thomasdevine01/cmkc-keyboard/Pages/Docs/Images/IMG-2283.jpg

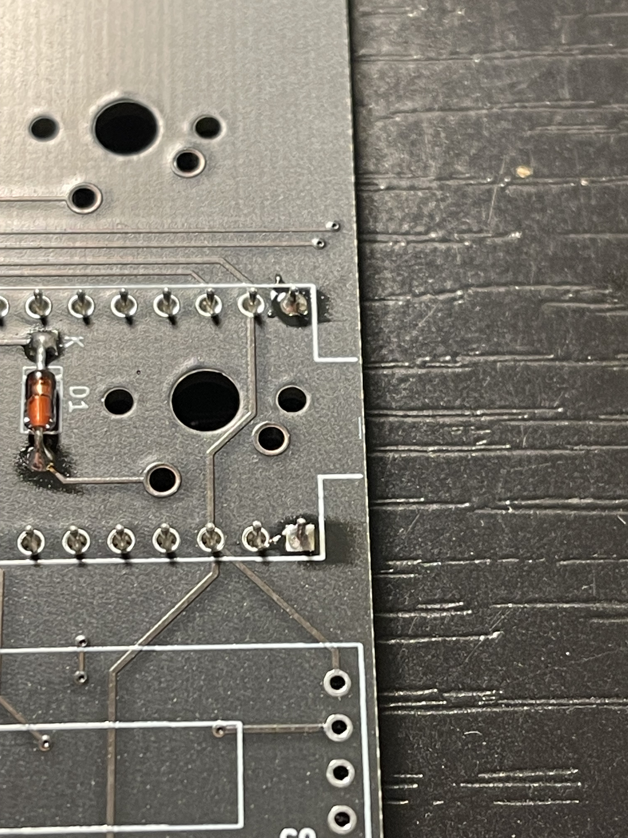
Pages/Docs/Images/IMG-2283.jpg
