thomasdevine01/cmkc-keyboard/Pages/Docs/Images/IMG-2287.jpg

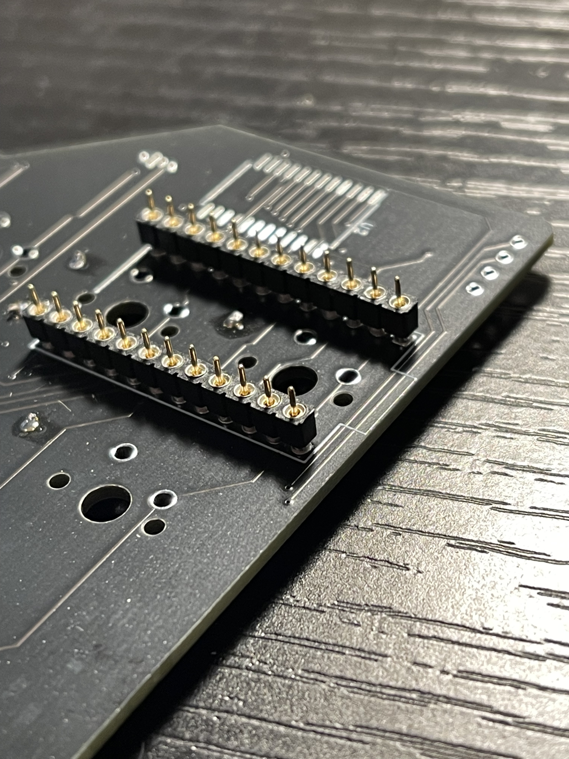
Pages/Docs/Images/IMG-2287.jpg
