thomasdevine01/cmkc-keyboard/Pages/Docs/Images/IMG-2662.jpg

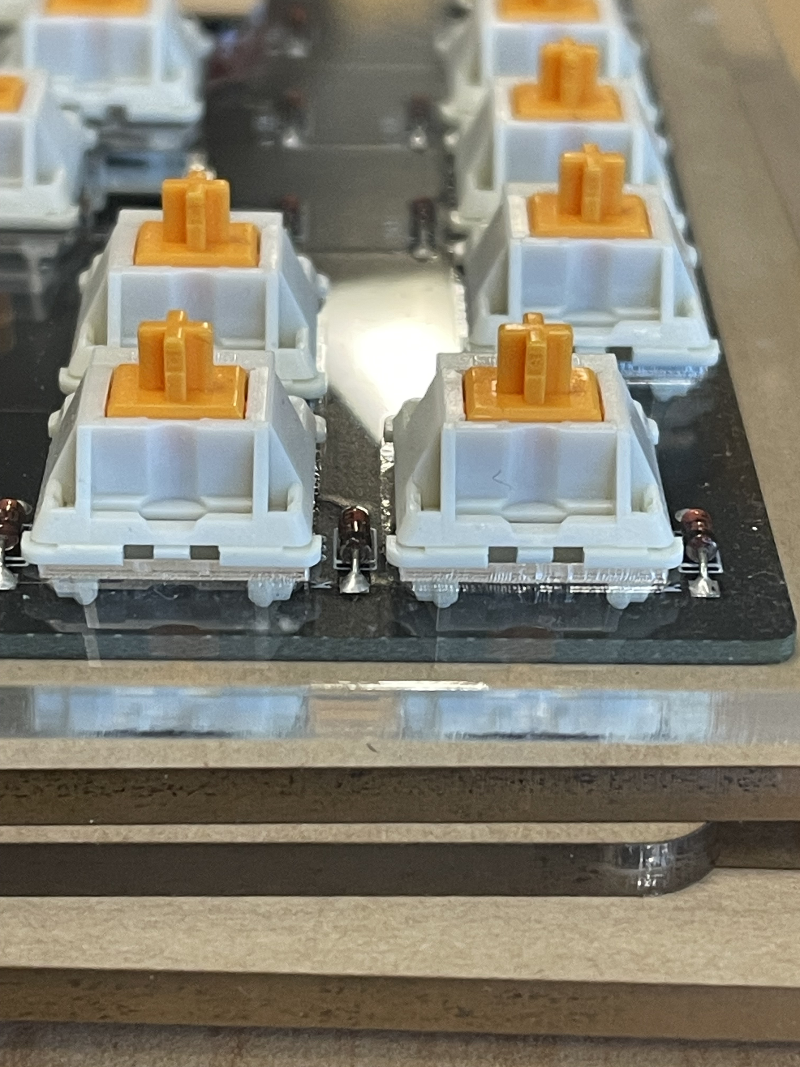
Pages/Docs/Images/IMG-2662.jpg
