thomasdevine01/cmkc-keyboard/Pages/Docs/Images/IMG-2682.jpg

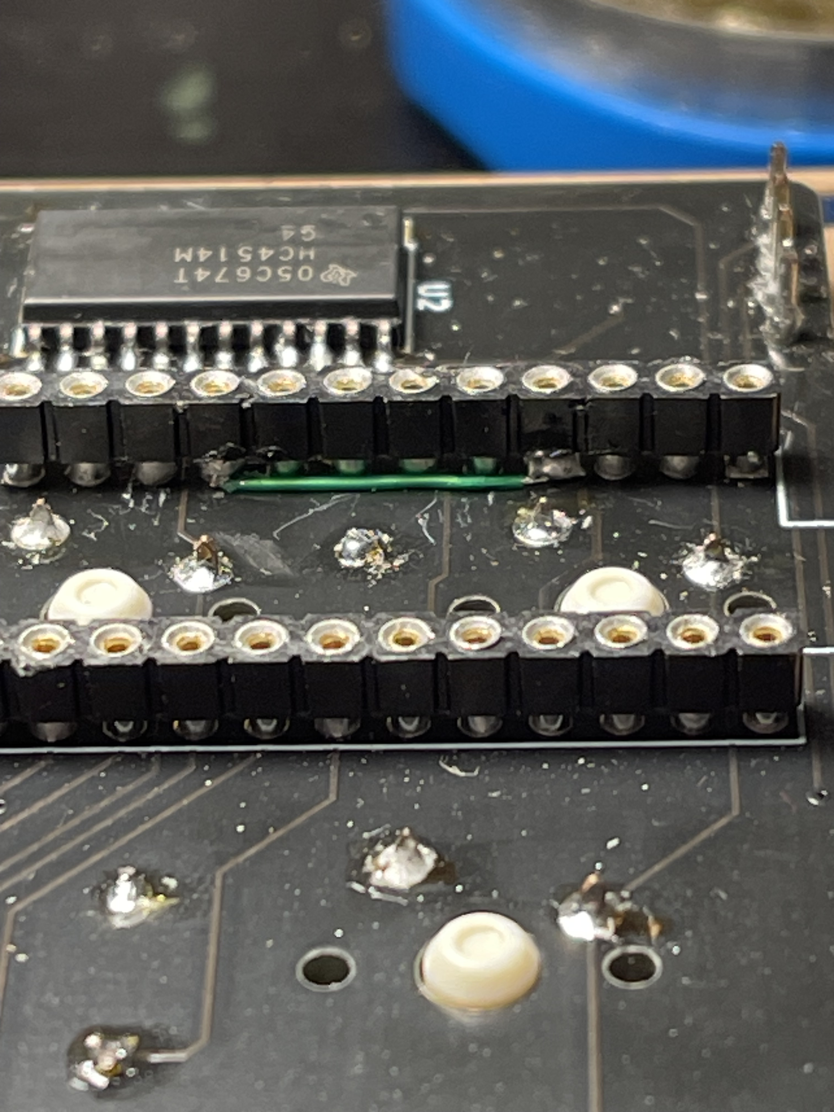
Pages/Docs/Images/IMG-2682.jpg
