thomasdevine01/cmkc-keyboard/Pages/Docs/Images/diodes-clipped.jpg

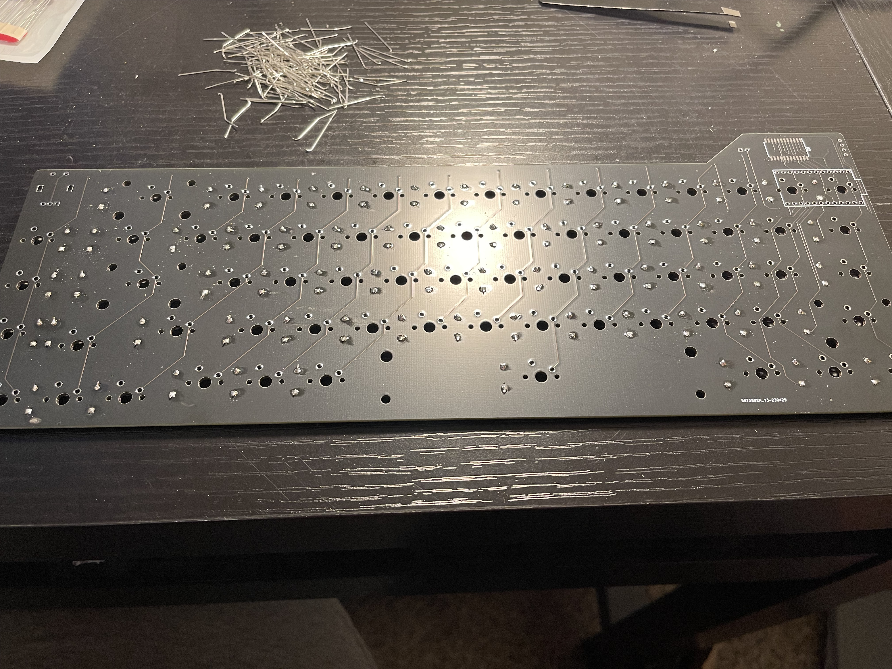
Pages/Docs/Images/diodes-clipped.jpg
