thomasdevine01/cmkc-keyboard/Pages/Docs/Images/IMG-2649.jpg

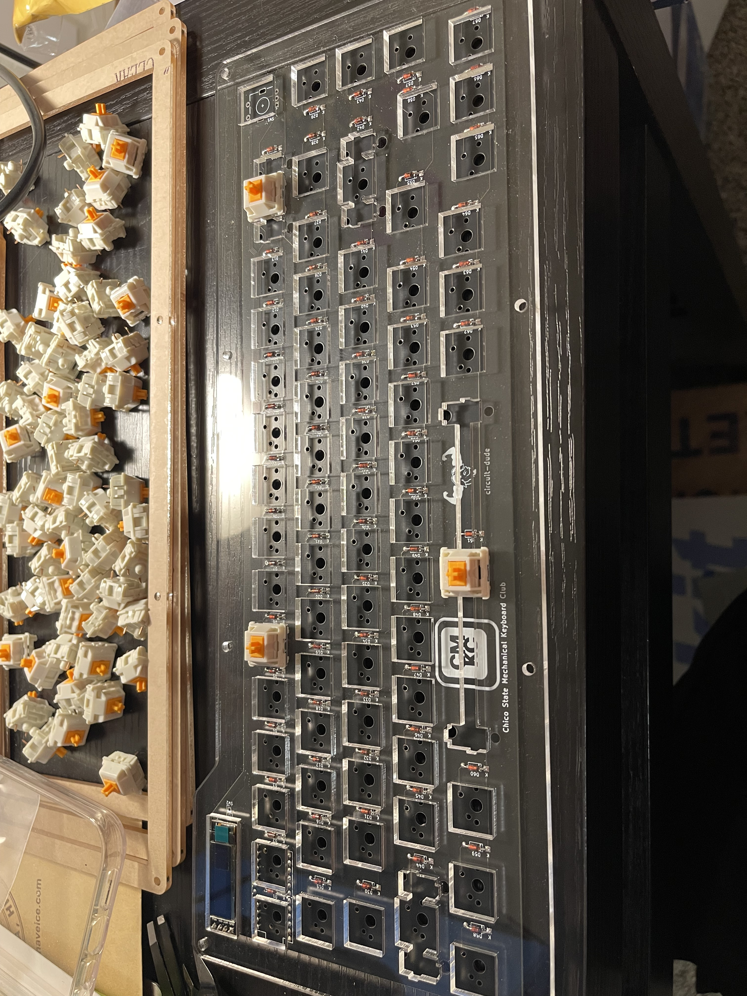
Pages/Docs/Images/IMG-2649.jpg
