thomasdevine01/cmkc-keyboard/Pages/Docs/Images/pcb-with-diodes.jpg

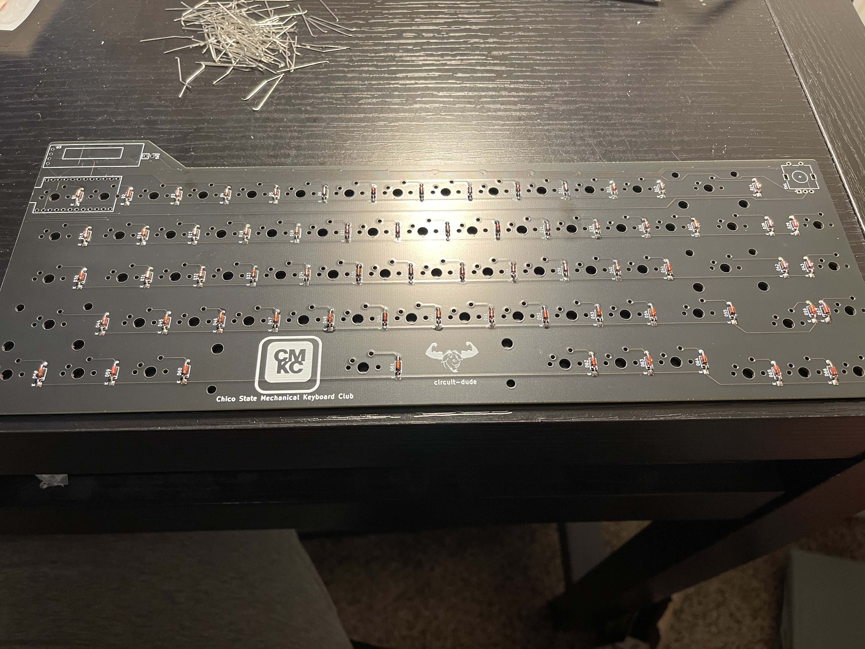
Pages/Docs/Images/pcb-with-diodes.jpg
